lhm0/DAB_minimalist/images/yt1.jpeg

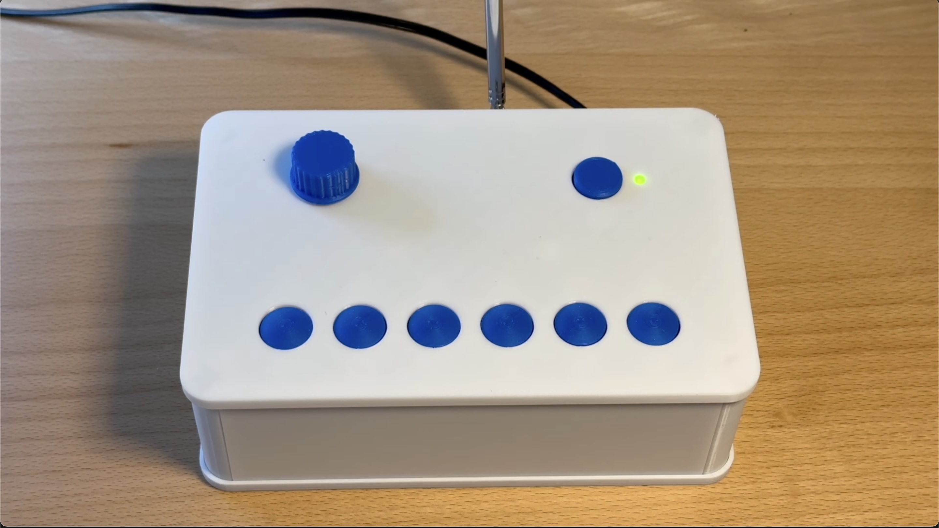
images/yt1.jpeg
