lhm0/DAB_minimalist/software/src/FileFunctions.h

#include <Arduino.h>
#include "FS.h"
#include <LittleFS.h>
#include <ArduinoJson.h>

void listDir(fs::FS &fs, const char *dirname, uint8_t levels);
void createDir(fs::FS &fs, const char *path);
void removeDir(fs::FS &fs, const char *path);
String readFile(fs::FS &fs, const char *path);
bool writeFile(fs::FS &fs, const char *path, const char *message);
void appendFile(fs::FS &fs, const char *path, const char *message);
void renameFile(fs::FS &fs, const char *path1, const char *path2);
void deleteFile(fs::FS &fs, const char *path);
void saveJsonToFile(fs::FS &fs, const char* filename, JsonDocument& doc);
void loadJsonFromFile(fs::FS &fs,const char* filename, JsonDocument& doc);
